TheHolyQuail/specialCharacterKeypad/keypad-ECAD.sch

## EAGLE design keypad-ECAD.sch (2021-03-21)

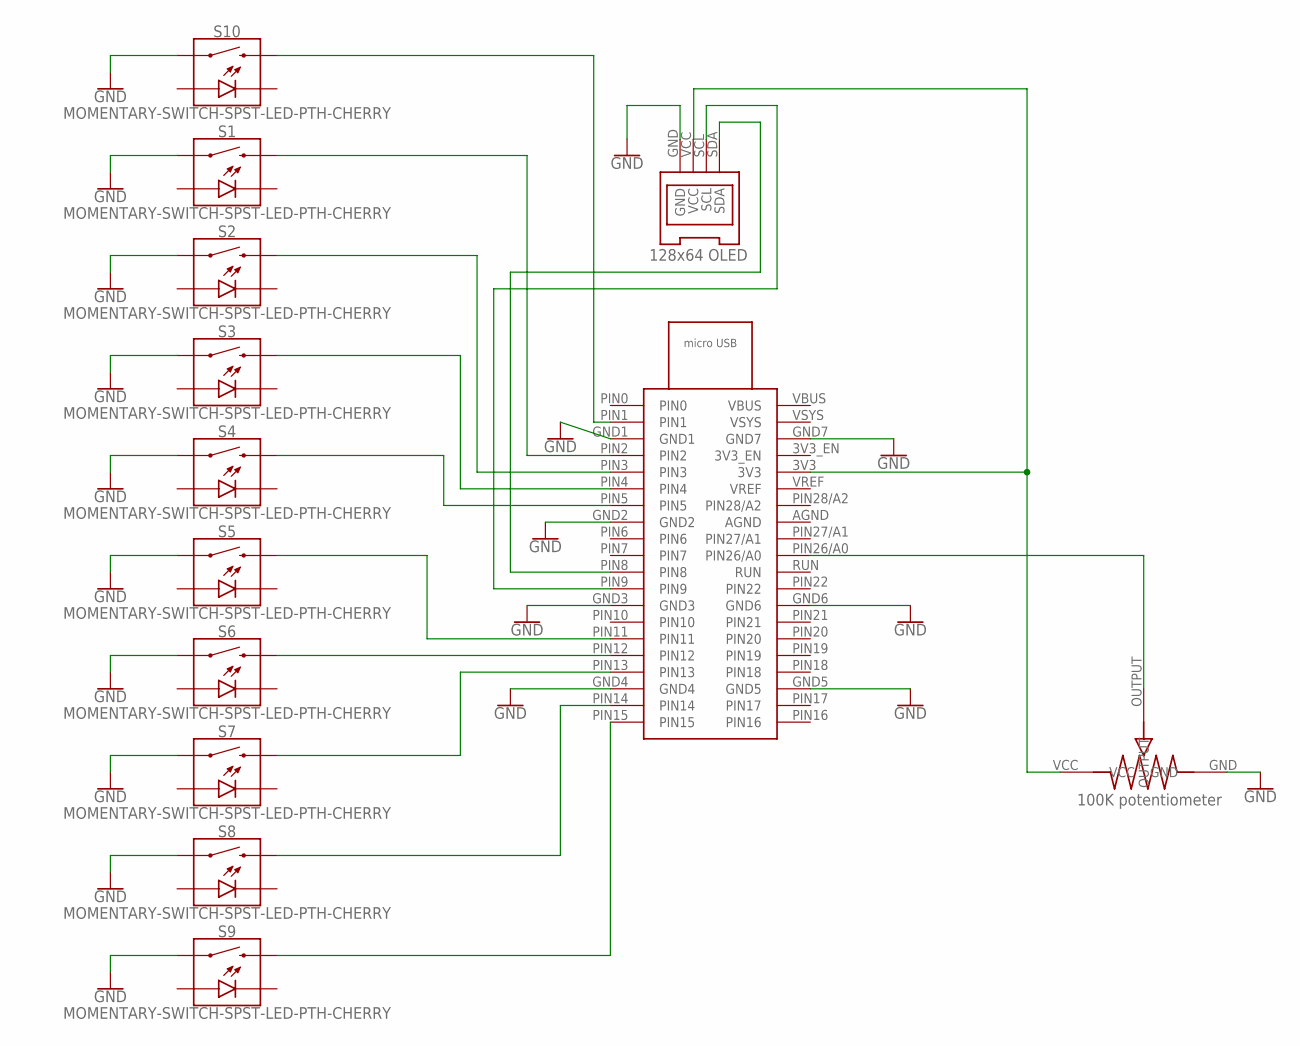
[picture p4: schematic keypad-ECAD.sch]

Parts:
S1, S2, S3, S4, S5, S6, S7, S8, S9, S10: MOMENTARY-SWITCH-SPST-LED-PTH-CHERRY; CHERRY-MX-LED
U$1: RP-PICO
U$2: 128X64-I2C-OLED
U$3: KEYPAD_POT

Connections:
GND: S1.S1 (1), S2.S1 (1), S3.S1 (1), S4.S1 (1), S5.S1 (1), S6.S1 (1), S7.S1 (1), S8.S1 (1), S9.S1 (1), S10.S1 (1), U$1.GND1, U$1.GND2, U$1.GND3, U$1.GND4, U$1.GND5, U$1.GND6, U$1.GND7, U$2.GND, U$3.GND
unnamed: S9.S2 (2), U$1.PIN15
unnamed: S8.S2 (2), U$1.PIN14
unnamed: S7.S2 (2), U$1.PIN13
unnamed: S6.S2 (2), U$1.PIN12
unnamed: S5.S2 (2), U$1.PIN11
unnamed: U$1.PIN8, U$2.SDA
unnamed: U$1.PIN9, U$2.SCL
unnamed: S4.S2 (2), U$1.PIN5
unnamed: S3.S2 (2), U$1.PIN4
unnamed: U$1.3V3, U$2.VCC, U$3.VCC
unnamed: U$1.PIN26/A0, U$3.OUTPUT
unnamed: S2.S2 (2), U$1.PIN3
unnamed: S1.S2 (2), U$1.PIN2
unnamed: S10.S2 (2), U$1.PIN1
